Polytech-Sorbonne/EI-SE5_2020-2021_ePet/CLOUD/SCHEMAS/Nouvelle trame - algo.jpg

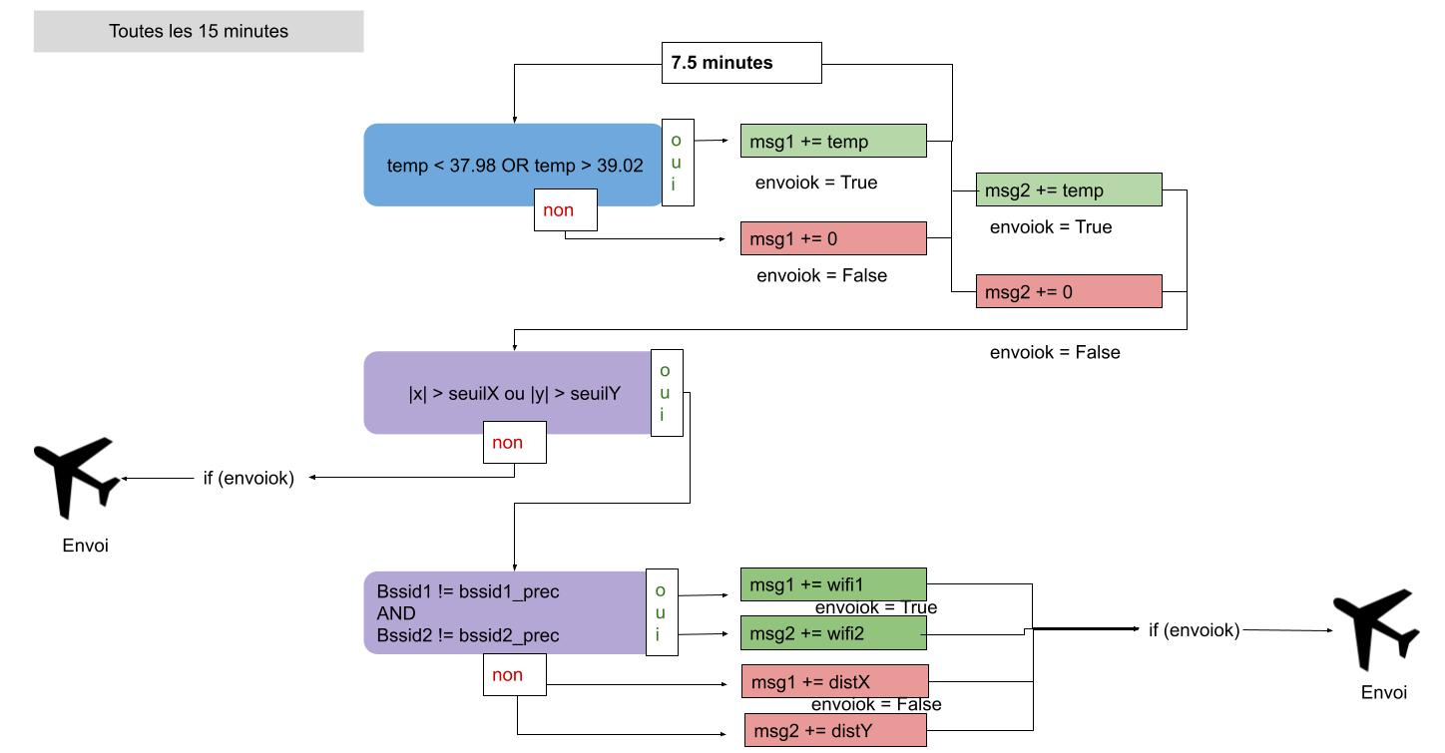
CLOUD/SCHEMAS/Nouvelle trame - algo.jpg
