Polytech-Sorbonne/EI-SE5_2020-2021_ePet/CLOUD/SCHEMAS/Trame complète.jpg

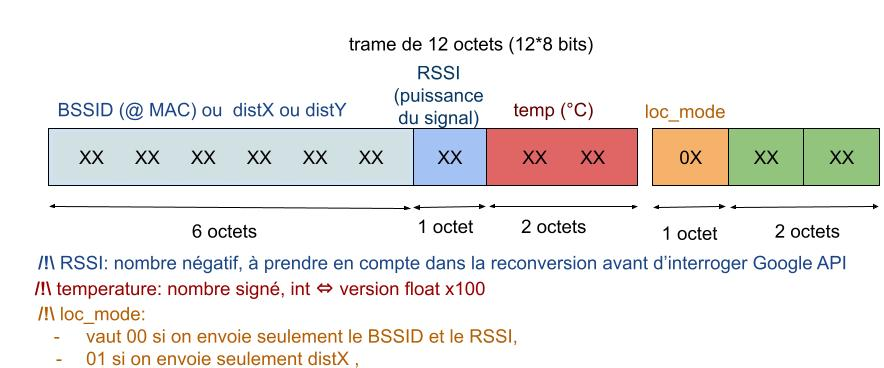
CLOUD/SCHEMAS/Trame complète.jpg
