Polytech-Sorbonne/EI-SE5_2020-2021_ePet/HARDWARE/PCB/CAPTEURS/Schema_pcb_capteur.PNG

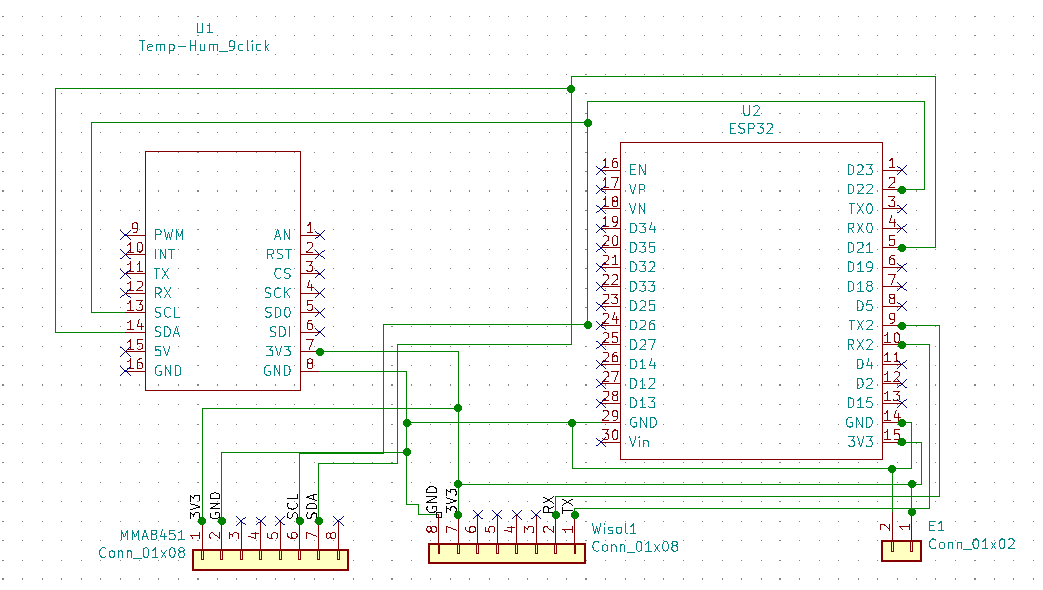
HARDWARE/PCB/CAPTEURS/Schema_pcb_capteur.PNG
