Polytech-Sorbonne/EI-SE5_2020-2021_ePet/HARDWARE/SCHEMAS_ELECTRONIQUES/SIGFOX/schema_branchement_wisol.png

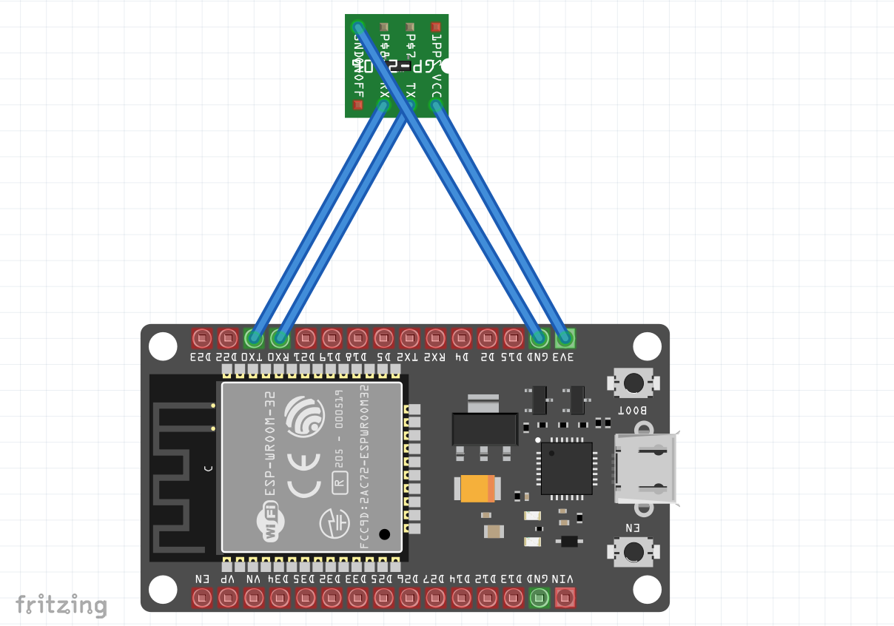
HARDWARE/SCHEMAS_ELECTRONIQUES/SIGFOX/schema_branchement_wisol.png
