Polytech-Sorbonne/EI-SE5_2020-2021_ePet/VISUELS/PCB.jpg

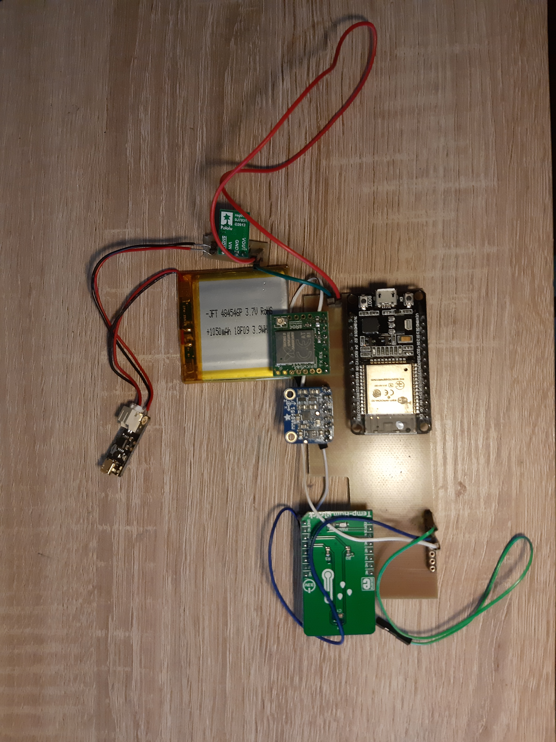
VISUELS/PCB.jpg
