Polytech-Sorbonne/EI-SE5_2020-2021_ePet/VISUELS/PCB_capteurs.jpg

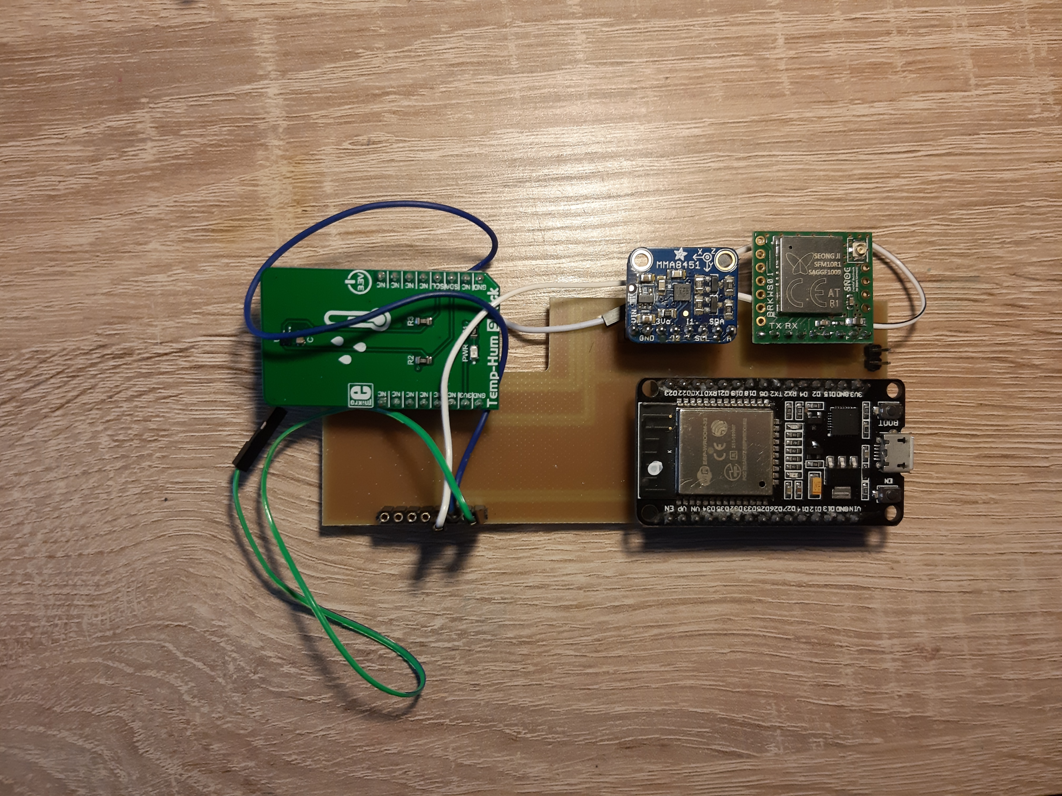
VISUELS/PCB_capteurs.jpg
