Polytech-Sorbonne/EI-SE5_2020-2021_ePet/CLOUD/SCHEMAS/Test des cas (ref switch code Arduino)_.jpg

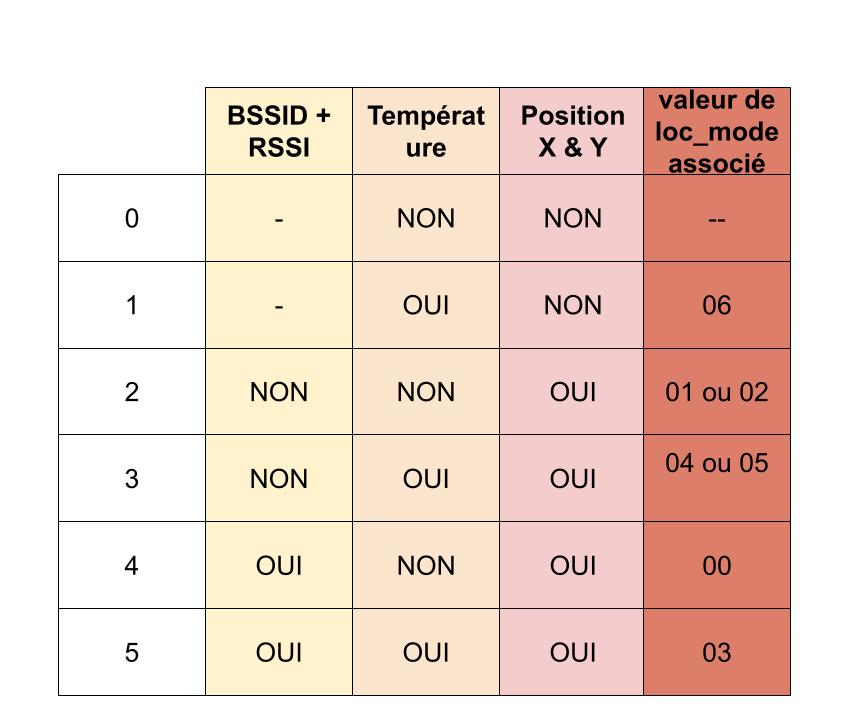
CLOUD/SCHEMAS/Test des cas (ref switch code Arduino)_.jpg
