Polytech-Sorbonne/EI-SE5_2020-2021_ePet/VISUELS/PCB_alim.jpg

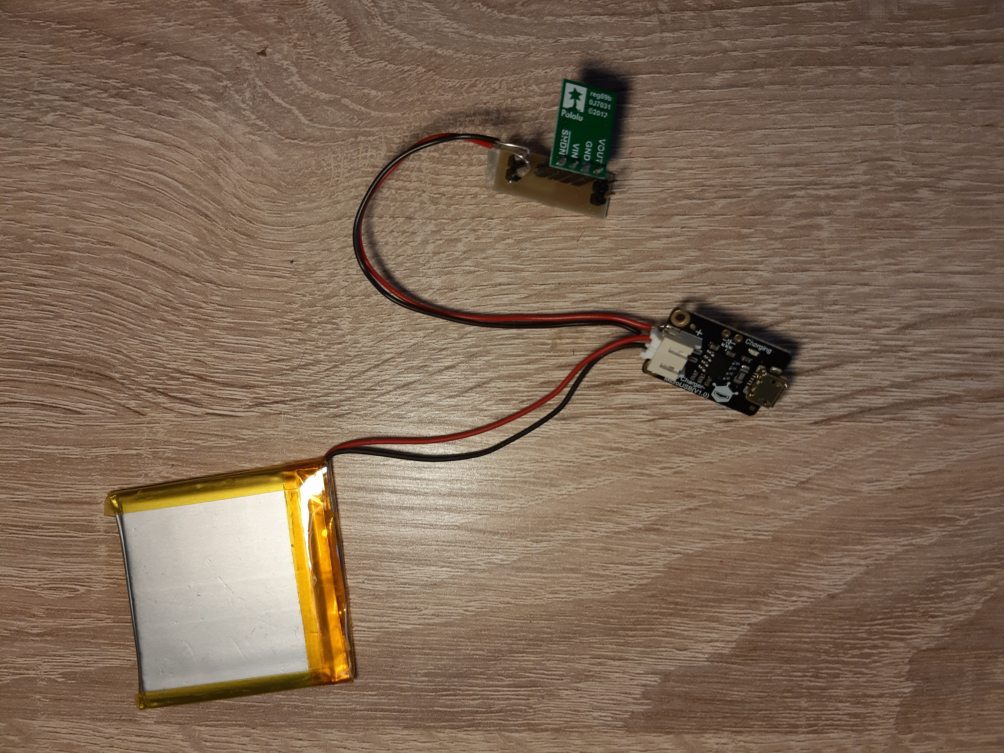
VISUELS/PCB_alim.jpg
